0x007E/ebs/EBS.asc

C1: EuropeanPolcap; 1F
C2: cap; 100n
C3: EuropeanPolcap; 10µ
D5: schottky; 1N5817
D6: LED; Red
Q1: npn; BC547C
Q2: pnp; BC557C
R1: EuropeanResistor; 10Meg
R2: EuropeanResistor; 10Meg
R3: EuropeanResistor; 4.7Meg
R4: EuropeanResistor; 33k
R5: EuropeanResistor; 10k
R6: EuropeanResistor; 1k
R7: EuropeanResistor; 1k
R8: EuropeanResistor; 1k
R9: EuropeanResistor; 10k
V1: voltage; 2V
Named nets: 0
.tran 10s
.MODEL Red D (IS=93.1P RS=42M N=5.6422 BV=4 IBV=10U CJO=2.97P VJ=.75 M=.333 TT=4.32U type=LED-red)
